gregdavill/boson-sd-hardware/hw/bosonFrameGrabber_1_01/output/renders/bosonFrameGrabber_1_01_3_3.png

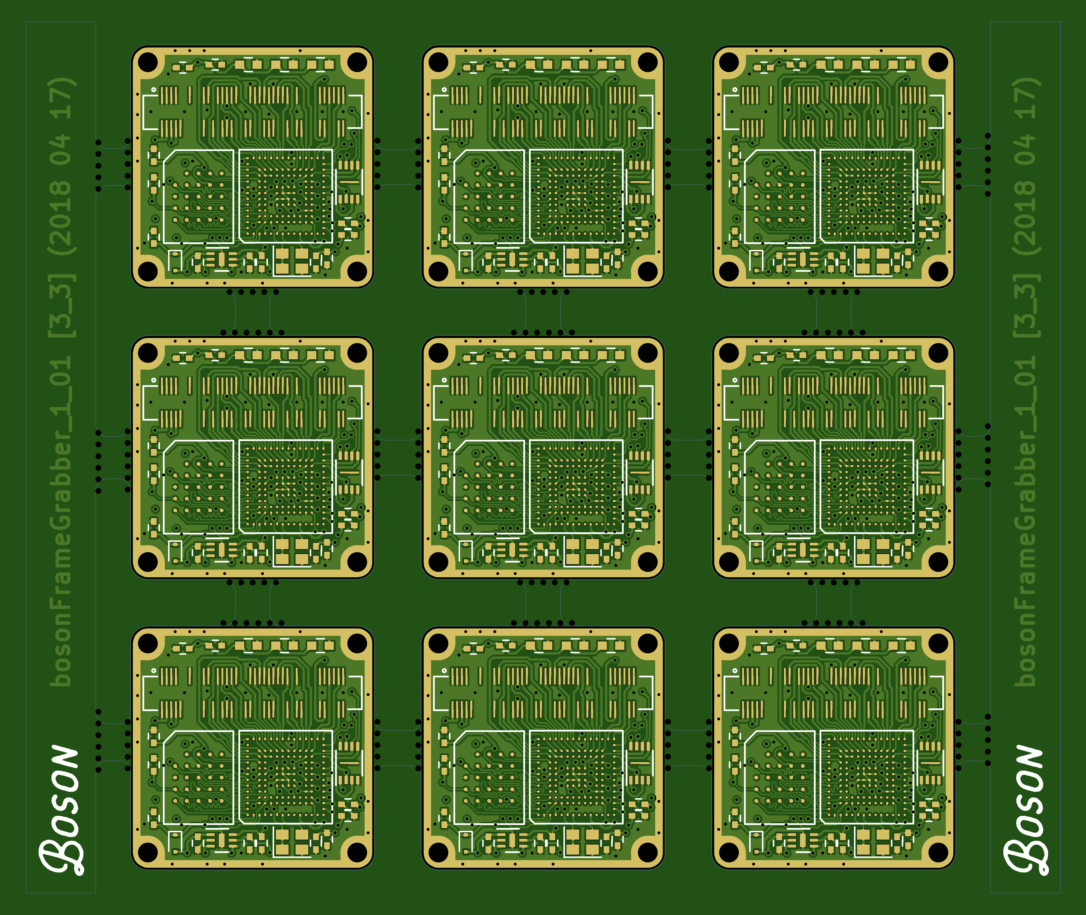
hw/bosonFrameGrabber_1_01/output/renders/bosonFrameGrabber_1_01_3_3.png
