gregdavill/boson-sd-hardware/hw/bosonFrameGrabber_1_02/output/renders/sch.png

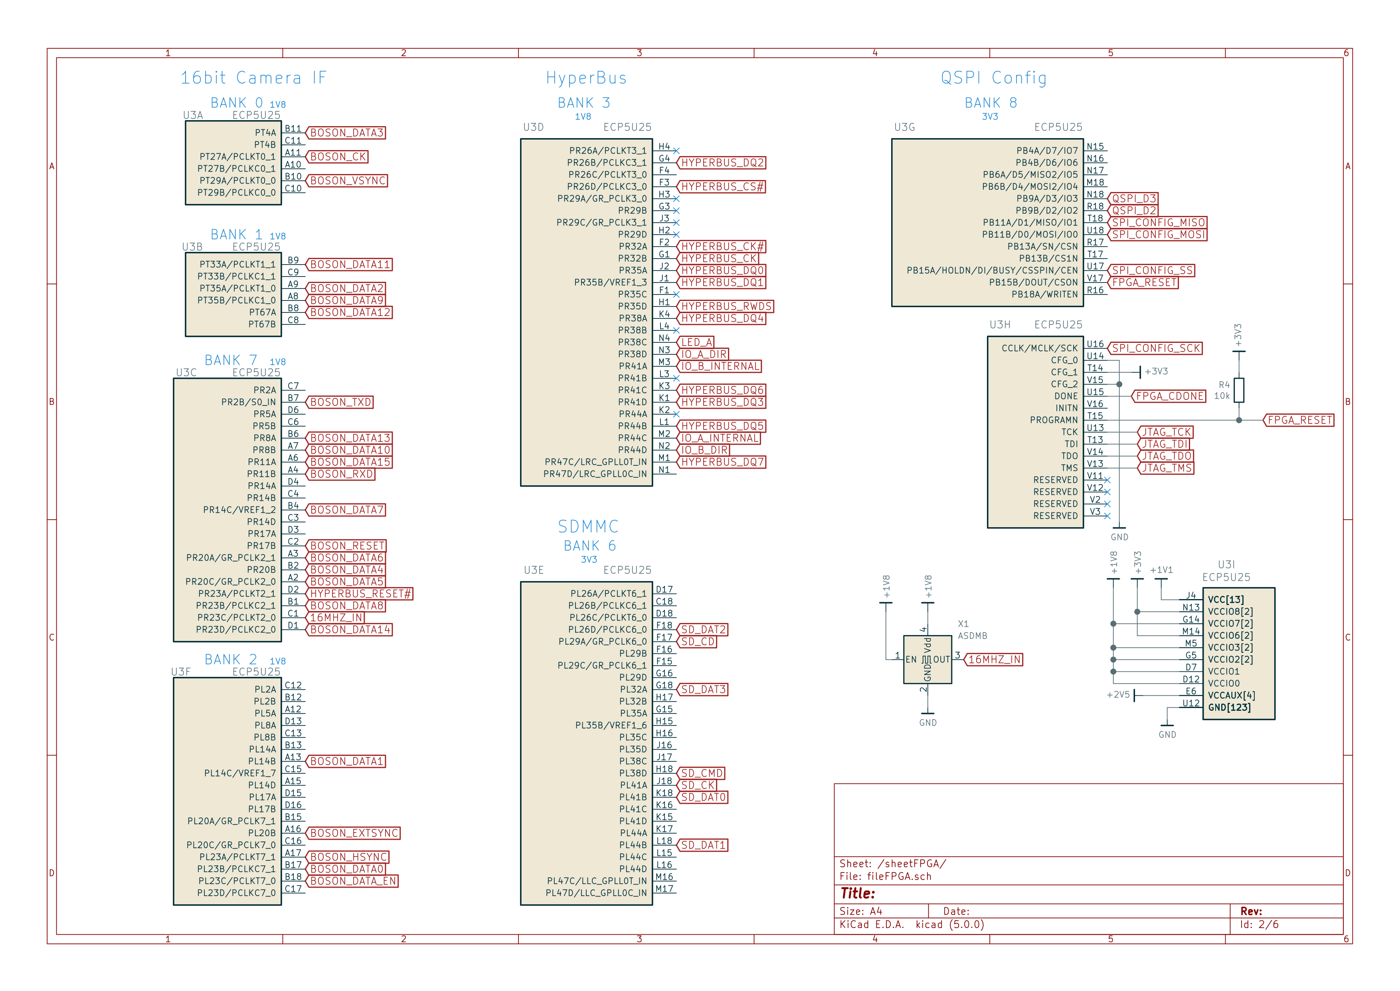
hw/bosonFrameGrabber_1_02/output/renders/sch.png
