gregdavill/boson-sd-hardware/hw/bosonFrameGrabber_1_02/3d/MicroSD.step

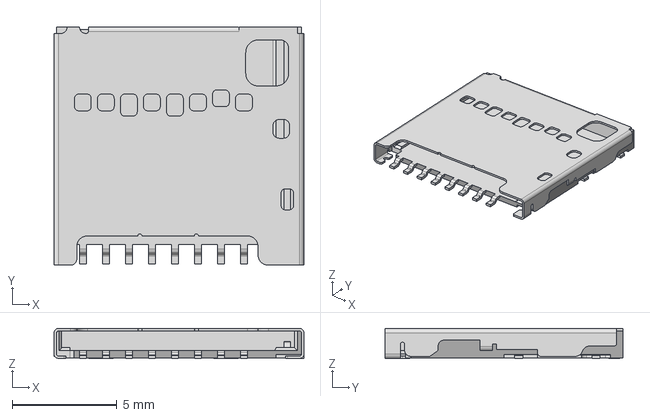
[picture p34: CAD file, 2018-04-01]
hw/bosonFrameGrabber_1_02/3d/MicroSD.step
11.9 x 11.4 x 1.45 mm
