gregdavill/boson-sd-hardware/hw/bosonFrameGrabber_1_00/output/renders/BosonFrameGrabber_assembly v1.png

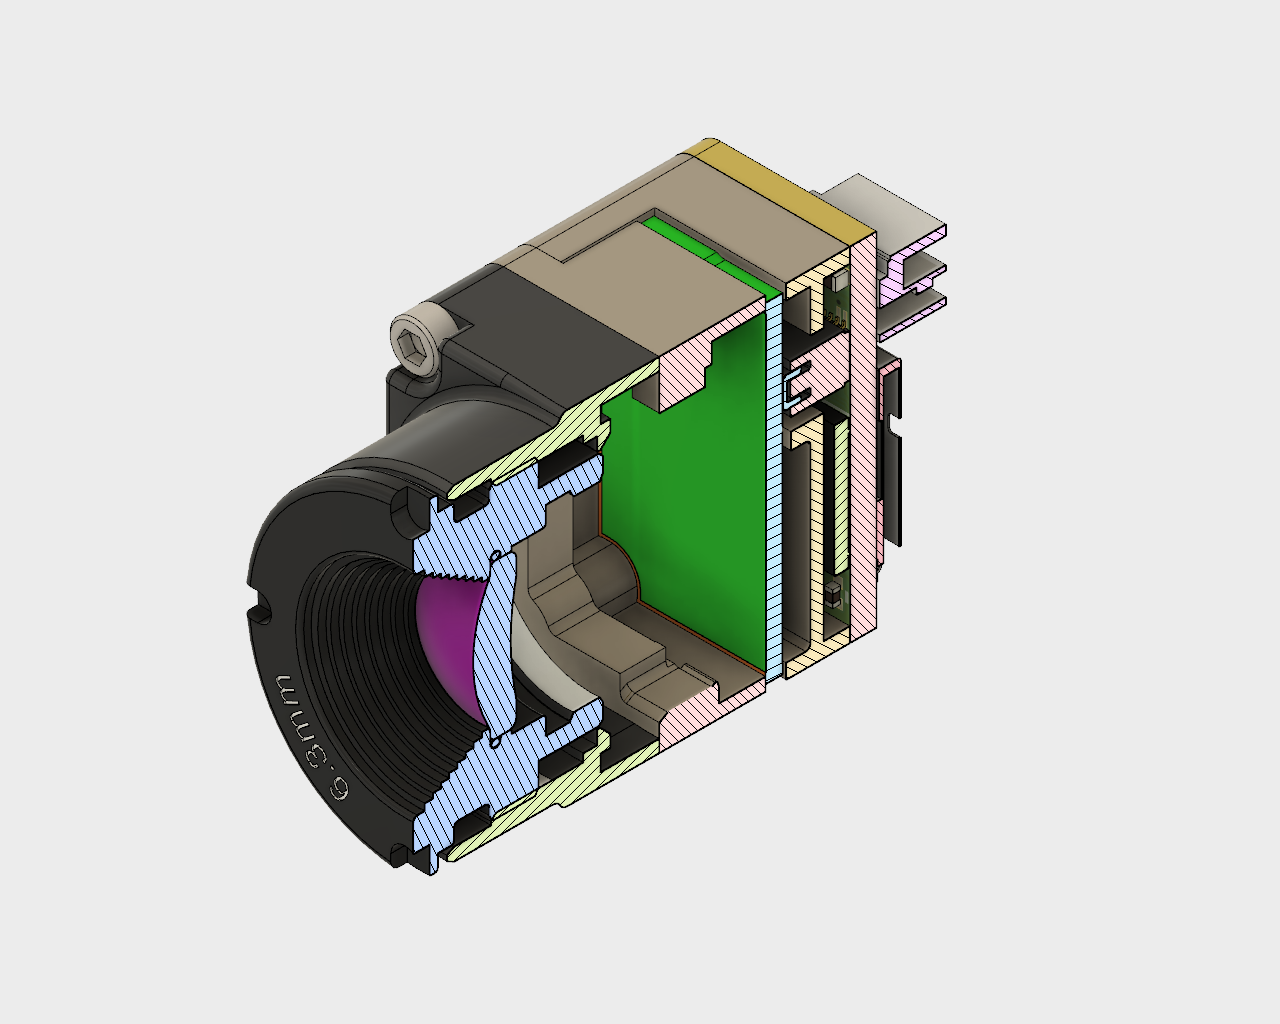
hw/bosonFrameGrabber_1_00/output/renders/BosonFrameGrabber_assembly v1.png
