gregdavill/boson-sd-hardware/hw/bosonFrameGrabber_1_00/output/renders/BosonFrameGrabber_assembly v3.png

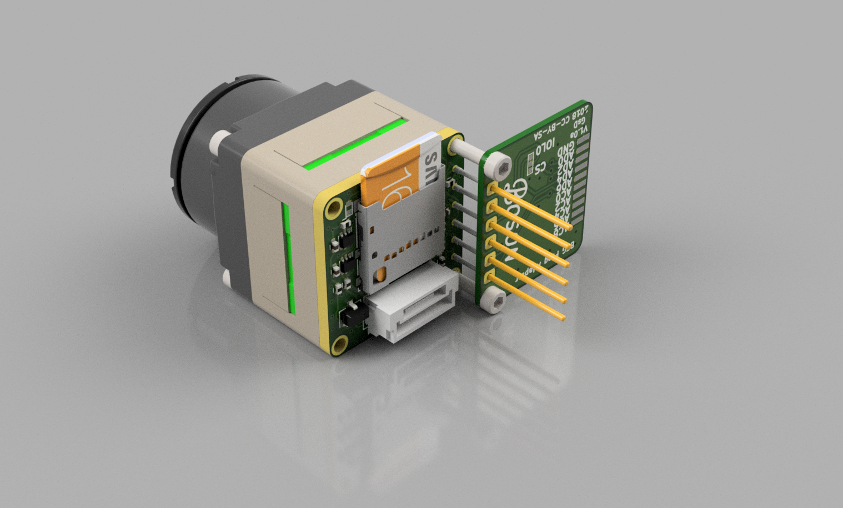
hw/bosonFrameGrabber_1_00/output/renders/BosonFrameGrabber_assembly v3.png
