gregdavill/boson-sd-hardware/hw/bosonFrameGrabber_1_00/output/renders/BosonFrameGrabber_assembly_001.jpg

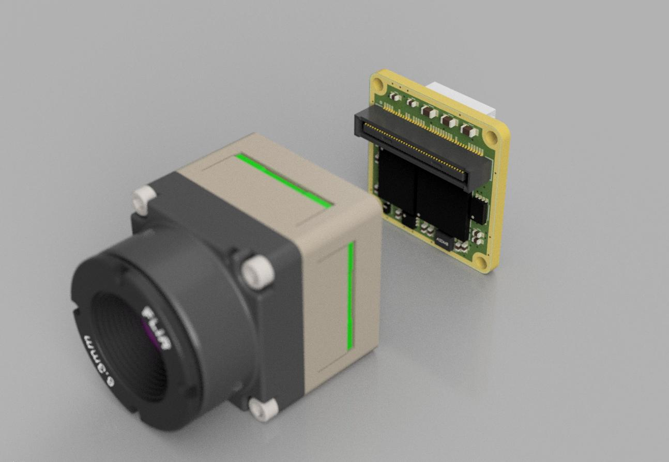
hw/bosonFrameGrabber_1_00/output/renders/BosonFrameGrabber_assembly_001.jpg
