gregdavill/boson-sd-hardware/hw/bosonFrameGrabber_1_02/output/panel/Test_3_3_Combined_Top.png

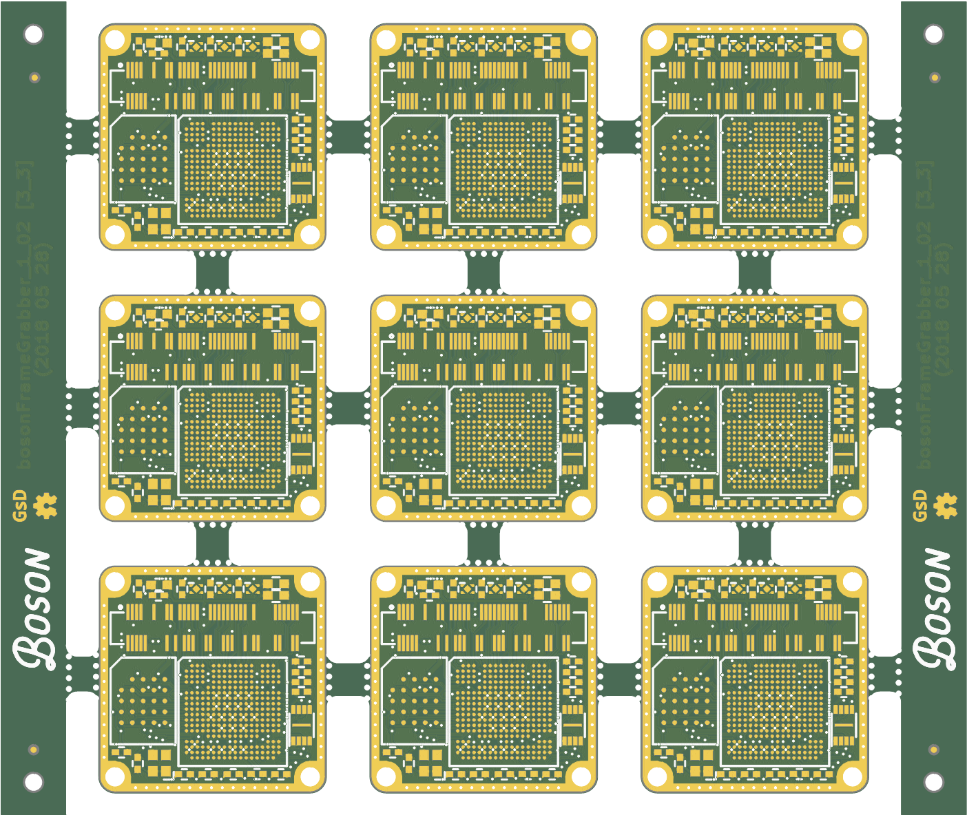
hw/bosonFrameGrabber_1_02/output/panel/Test_3_3_Combined_Top.png
